TobiasVanDyk/STM32F411-PCM5102A-24bit-USB-Audio-DAC/images/dac10.jpg

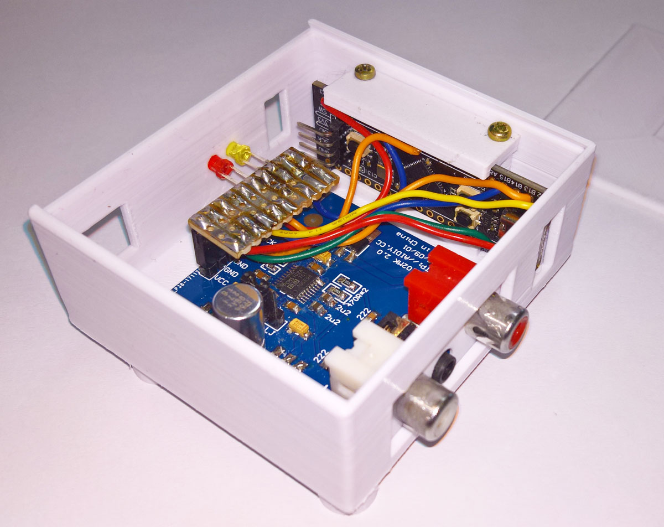
images/dac10.jpg
