TobiasVanDyk/STM32F411-PCM5102A-24bit-USB-Audio-DAC/images/SMD-LED-Resistor.png

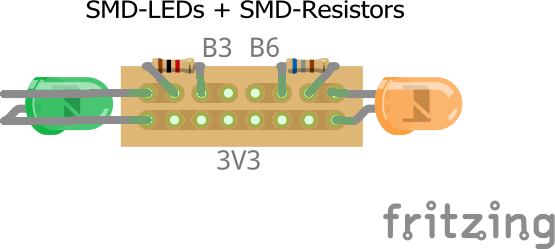
images/SMD-LED-Resistor.png
